shaimendel/BioTagMonitor/Simulation/limiter-reservoir-cap.asc

battery: battery; 3
internal: res; 10
leakage: res; 250K
limiter: res; 2000
load: bi; P=0.05*I(scheduler)
reservoir: cap; 330µ; Rser=0.05
scheduler: current; PULSE(0 1 1s 0 0 8ms 8 1000)
Vs: voltage; 1
Named nets: 0, Vbat, Vload
.tran 0 100s 0
.ic V(Vbat)=3 V(Vload)=3
 
.measure Pbat INTEG -I(battery)*V(Vbat)
.measure Pload INTEG I(load)*V(Vload)
.measure Plimiter INTEG I(limiter)*(V(Vbat)-V(Vload))
.measure Pleakage INTEG I(leakage)*V(Vload)
.measure Ecap param 0.5*330e-6*3*3-0.5*330e-6*V(Vload)*V(Vload) at=1000
 
.measure FracCap param Ecap/Pbat
.measure FracLoad param Pload/Pbat
.measure FracLimiter param Plimiter/Pbat
.measure FracLeakage param Pleakage/Pbat
.measure FracTotal param FracLoad+FracLimiter+FracLeakage+FracCap
 
.measure cFracCap param Ecap/Pbat
.measure cFracLoad param PLoad/(Pbat+Ecap)
.measure cFracLimiter param Plimiter/(Pbat+Ecap)
.measure cFracLeakage param Pleakage/(Pbat+Ecap)
.measure cFracTotal param cFracLoad+cFracLimiter+cFracLeakage
 
.measure Vmin MIN V(Vload)
replace P=0.05*I(scheduler)
with I=0.02*I(scheduler)
for constant current
